a-blue-pig/battlebot-2023/pictures/IMG_2284.jpeg

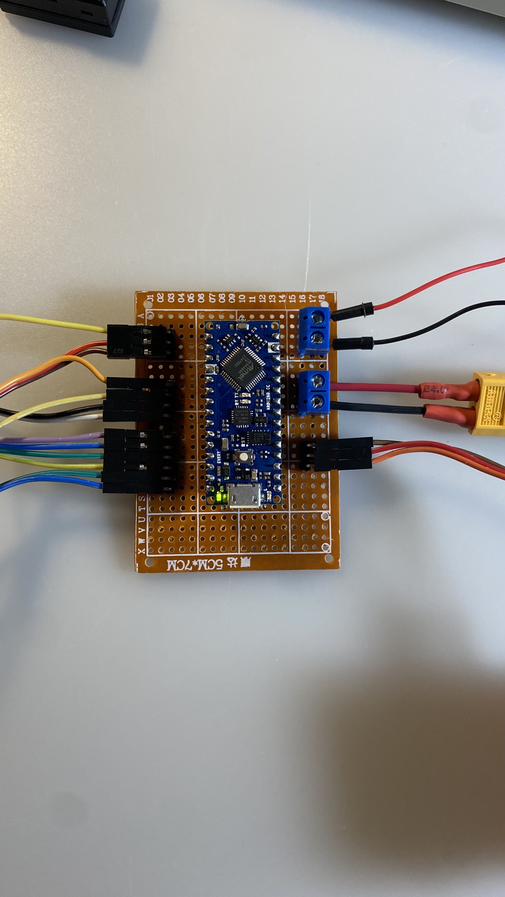
pictures/IMG_2284.jpeg
