a-blue-pig/battlebot-2023/pictures/IMG_2332.jpeg

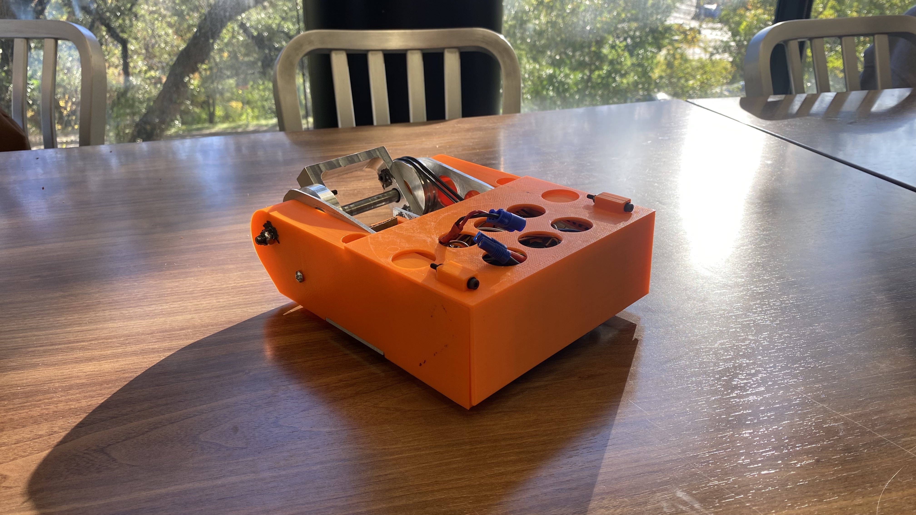
pictures/IMG_2332.jpeg
